TSS5960/AI_IR_Remote/ir_control.cpp

#include "ir_control.h"

// Initialize IR receiver with larger buffer for complex protocols (AC remotes can be very long, It can't be learnt)
const uint16_t kCaptureBufferSize = 1024;  // Increased from default ~300
const uint8_t kTimeout = 50;  // Timeout in milliseconds (50ms default)
const uint16_t kFrequency = 38000;  // 38kHz modulation frequency

IRsend irsend(IR_TX_PIN);
IRrecv irrecv(IR_RX_PIN, kCaptureBufferSize, kTimeout, true);
decode_results results;

IRDaikinESP daikinAC(IR_TX_PIN);
IRMitsubishiAC mitsubishiAC(IR_TX_PIN);
IRPanasonicAc panasonicAC(IR_TX_PIN);
IRGreeAC greeAC(IR_TX_PIN);
IRMideaAC mideaAC(IR_TX_PIN);
IRHaierAC haierAC(IR_TX_PIN);
IRSamsungAc samsungAC(IR_TX_PIN);
IRLgAc lgAC(IR_TX_PIN);
IRFujitsuAC fujitsuAC(IR_TX_PIN);
IRHitachiAc hitachiAC(IR_TX_PIN);

void initIR() {
  irsend.begin();
  irrecv.enableIRIn();
  
  daikinAC.begin();
  mitsubishiAC.begin();
  panasonicAC.begin();
  greeAC.begin();
  mideaAC.begin();
  haierAC.begin();
  samsungAC.begin();
  lgAC.begin();
  fujitsuAC.begin();
  hitachiAC.begin();
  
  Serial.printf("IR Transmitter Initialization complete (GPIO%d)\n", IR_TX_PIN);
  Serial.printf("IR Receiver Initialization complete (GPIO%d)\n", IR_RX_PIN);
}

uint8_t convertMode(ACMode mode) {
  switch(mode) {
    case MODE_AUTO: return 0;
    case MODE_COOL: return 1;
    case MODE_HEAT: return 2;
    case MODE_DRY:  return 3;
    case MODE_FAN:  return 4;
    default: return 1;
  }
}

uint8_t convertFanSpeed(FanSpeed speed) {
  switch(speed) {
    case FAN_AUTO: return 0;
    case FAN_LOW:  return 1;
    case FAN_MED:  return 2;
    case FAN_HIGH: return 3;
    default: return 0;
  }
}

void sendACState(const ACState& state) {
  Serial.println("\n[IR] Sending AC state...");
  Serial.printf("     Brand: %s\n", getBrandName(state.brand));
  Serial.printf("     Power: %s\n", state.power ? "ON" : "OFF");
  Serial.printf("     Temp: %dC\n", state.temperature);
  
  switch(state.brand) {
    case BRAND_DAIKIN:
      daikinAC.setPower(state.power);
      daikinAC.setTemp(state.temperature);
      daikinAC.setMode(convertMode(state.mode));
      daikinAC.setFan(convertFanSpeed(state.fanSpeed));
      daikinAC.send();
      Serial.println("     -> Daikin signal sent");
      break;
      
    case BRAND_MITSUBISHI:
      mitsubishiAC.setPower(state.power);
      mitsubishiAC.setTemp(state.temperature);
      mitsubishiAC.setMode(convertMode(state.mode));
      mitsubishiAC.setFan(convertFanSpeed(state.fanSpeed));
      mitsubishiAC.send();
      Serial.println("     -> Mitsubishi signal sent");
      break;
      
    case BRAND_PANASONIC:
      panasonicAC.setPower(state.power);
      panasonicAC.setTemp(state.temperature);
      panasonicAC.setMode(convertMode(state.mode));
      panasonicAC.setFan(convertFanSpeed(state.fanSpeed));
      panasonicAC.send();
      Serial.println("     -> Panasonic signal sent");
      break;
      
    case BRAND_GREE:
      greeAC.setPower(state.power);
      greeAC.setTemp(state.temperature);
      greeAC.setMode(convertMode(state.mode));
      greeAC.setFan(convertFanSpeed(state.fanSpeed));
      greeAC.send();
      Serial.println("     -> Gree signal sent");
      break;
      
    case BRAND_MIDEA:
      mideaAC.setPower(state.power);
      mideaAC.setTemp(state.temperature);
      mideaAC.setMode(convertMode(state.mode));
      mideaAC.setFan(convertFanSpeed(state.fanSpeed));
      mideaAC.send();
      Serial.println("     -> Midea signal sent");
      break;
      
    case BRAND_HAIER:
      haierAC.setCommand(state.power ? kHaierAcCmdOn : kHaierAcCmdOff);
      haierAC.setTemp(state.temperature);
      haierAC.setMode(convertMode(state.mode));
      haierAC.setFan(convertFanSpeed(state.fanSpeed));
      haierAC.send();
      Serial.println("     -> Haier signal sent");
      break;
      
    case BRAND_SAMSUNG:
      samsungAC.setPower(state.power);
      samsungAC.setTemp(state.temperature);
      samsungAC.setMode(convertMode(state.mode));
      samsungAC.setFan(convertFanSpeed(state.fanSpeed));
      samsungAC.send();
      Serial.println("     -> Samsung signal sent");
      break;
      
    case BRAND_LG:
      lgAC.setPower(state.power);
      lgAC.setTemp(state.temperature);
      lgAC.setMode(convertMode(state.mode));
      lgAC.setFan(convertFanSpeed(state.fanSpeed));
      lgAC.send();
      Serial.println("     -> LG signal sent");
      break;
      
    case BRAND_FUJITSU:
      fujitsuAC.setPower(state.power);
      fujitsuAC.setTemp(state.temperature);
      fujitsuAC.setMode(convertMode(state.mode));
      fujitsuAC.setFanSpeed(convertFanSpeed(state.fanSpeed));
      fujitsuAC.send();
      Serial.println("     -> Fujitsu signal sent");
      break;
      
    case BRAND_HITACHI:
      hitachiAC.setPower(state.power);
      hitachiAC.setTemp(state.temperature);
      hitachiAC.setMode(convertMode(state.mode));
      hitachiAC.setFan(convertFanSpeed(state.fanSpeed));
      hitachiAC.send();
      Serial.println("     -> Hitachi signal sent");
      break;
      
    default:
      Serial.println("     WARN: Unknown brand, using Daikin default");
      daikinAC.setPower(state.power);
      daikinAC.setTemp(state.temperature);
      daikinAC.send();
      break;
  }
  
  delay(100);
  
  // Resume IR receiver after sending (sending pauses it)
  irrecv.resume();
  Serial.println("[IR] IR receiver resumed after transmission");
}
